gazzmaniac/Amiga-SMD-500/SMD500.sch

## KiCad design SMD500.sch (2019-11-12)

Schematic: SMD500.sch

Parts:
BT9: COINCELL; SMTU2032LF
C1, C2, C3, C4, C5, C6, C9, C11, C13, C14, C16, C17, C18, C19, C20, C21, C22, C23, C40, C41, C42, C301, C302, C305, C325, C335, C501, C502, C804: 0.33 uF; C_0805_2012Metric_Pad1.15x1.40mm_HandSolder
C7, C8, C10, C12, C15, C32, C33, C33.1, C34, C35, C36, C37, C39, C308, C701, C713, C800, C801, C802, C803: 0.01 uF; C_0805_2012Metric_Pad1.15x1.40mm_HandSolder
C45.1, C306, C712: 10 uF; CP_Elec_4x5.7
C45.2, C45.3, C321, C331, C450, C451, C711: 0.1 uF; C_0805_2012Metric_Pad1.15x1.40mm_HandSolder
C298, C299: 0.47 uF; C_0805_2012Metric_Pad1.15x1.40mm_HandSolder
C303, C304, C324, C334: 22 uF; CP_Elec_6.3x5.3
C307, C401, C402: 1000 uF; CAPAE1350X1400N
C311, C312, C313, C314: 0.047 uF; C_0805_2012Metric_Pad1.15x1.40mm_HandSolder
C322, C332: 6800 pF; C_0805_2012Metric_Pad1.15x1.40mm_HandSolder
C323, C333: 3900 pF; C_0805_2012Metric_Pad1.15x1.40mm_HandSolder
C403: 47 pF; C_0805_2012Metric_Pad1.15x1.40mm_HandSolder
C411, C412, C413, C421, C422, C423: 470 pF; C_0805_2012Metric_Pad1.15x1.40mm_HandSolder
C452: 0.1u; C_0805_2012Metric_Pad1.15x1.40mm_HandSolder
C453: 18 pF; C_0805_2012Metric_Pad1.15x1.40mm_HandSolder
C460: 33 pF; C_0805_2012Metric_Pad1.15x1.40mm_HandSolder
C461: 39 pF; C_0805_2012Metric_Pad1.15x1.40mm_HandSolder
C811, C812, C813, C814, C815, C816: 100 uF; CP_Elec_6.3x7.7
C821, C822: 47 uF; CP_Elec_6.3x7.7
C911: 22 pF; C_0805_2012Metric_Pad1.15x1.40mm_HandSolder
C913: 4.7 uF; EEEHB1E4R7AR
CE101, CE110, CE402, CE403, CE404, CE405, CE407, CE498, CE501, CE531, CE601, CE602, CE702, CE703, CE704: 0.01 uF; C_0805_2012Metric_Pad1.15x1.40mm_HandSolder
CE104, CE105: 68 pF; C_0805_2012Metric_Pad1.15x1.40mm_HandSolder
CE302, CE303, CE411, CE412, CE413, CE414, CE421, CE422, CE423, CE424: 6800 pF; C_0805_2012Metric_Pad1.15x1.40mm_HandSolder
CE401, CE408: 0.22 uF; C_0805_2012Metric_Pad1.15x1.40mm_HandSolder
CE402.2, CE402.3, CE402.4, CE402.5, CE403.1, CE403.3, CE403.4, CE431, CE432, CE433, CE434, CE499, CE511, CE512, CE513, CE514, CE515, CE516, CE517, CE518, CE519, CE521, CE522, CE523, CE524, CE525, CE532, CE533, CE534, CE535, CE536, CE537, CE538, CE611, CE612, CE613, CE614, CE615, CE616, CE617, CE618, CE619, CE620, CE621, CE622, CE623, CE624, CE625, CE626: 100 pF; C_0805_2012Metric_Pad1.15x1.40mm_HandSolder
CE441, CE442, CE443, CE444: 470 pF; C_0805_2012Metric_Pad1.15x1.40mm_HandSolder
CN1, CN2: DB9-M; D09P13B4PA00LF; MPN 5747840-3; Mouser Product D09P13B4PA00LF
CN3: PJRAN1X1U03AUX(RED); PJRAN1X1U03AUX; Mouser Part Number 502-PJRAN1X1U03AUX
CN4: PJRAN1X1U02AUX(WHITE); PJRAN1X1U03AUX; Mouser Part Number 502-PJRAN1X1U03AUX
CN5: DB23_Female_MountingHoles; DSUB-23_Female_Horizontal_P2.77x2.84mm_EdgePinOffset4.94mm_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
CN6: DB25P; D25P13B4PA00LF
CN7: DB25S; D25S33E4PA00LF
CN8: SQ&RNDDIN; A500 Power
CN9: DB23; DSUB-23_Male_Horizontal_P2.77x2.84mm_EdgePinOffset4.94mm_Ho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
CN10: PJRAN1X1U03AUX(YELLOW); PJRAN1X1U03AUX; Mouser Part Number 502-PJRAN1X1U03AUX
CN11: 2x17; PinHeader_2x17_P2.54mm_Vertical
CN12, CN14: 2-171825-4; TE_2-171825-4
CN13: 1x8HEADER; PinHeader_1x08_P2.54mm_Vertical
CN15, CN45: Conn_01x04; HDRV4W69P0X250_1X4_1000X500X1040P
D99, D912: 1N4148W-7-F; SOD3716X115N; Manufacturer_Part_Number 1N4148W-7-F; Mouser Part Number 621-1N4148W-F
D501: 1N914; D_DO-35_SOD27_P7.62mm_Horizontal
E101, E110, E402, E403, E404, E405, E406.1, E406.2, E407, E431, E432, E433, E498: FB200R; R_0805_2012Metric_Pad1.15x1.40mm_HandSolder
E102, E103, E106, E107, E108, E109: 47 pF; C_0805_2012Metric_Pad1.15x1.40mm_HandSolder
E305, E306: 270 pF; C_0805_2012Metric_Pad1.15x1.40mm_HandSolder
E435: FB; R_0805_2012Metric_Pad1.15x1.40mm_HandSolder
E501, E502, E503: 47R 0.5W; R_0805_2012Metric_Pad1.15x1.40mm_HandSolder
E631, E632: 100 pF; C_0805_2012Metric
E666: 22 pF; C_0805_2012Metric
E791, E792, E793, E794: 47 pF; C_0805_2012Metric
FB101: 68R@100MHz; R_0805_2012Metric_Pad1.15x1.40mm_HandSolder
FB102: 150R@100MHz; R_0805_2012Metric_Pad1.15x1.40mm_HandSolder
FB601, FB602, FB702, FB703, FB704: FB200R; R_0805_2012Metric_Pad1.15x1.40mm_HandSolder
FB802: FB; R_0805_2012Metric_Pad1.15x1.40mm_HandSolder
HY1: VIDEOHYBRID; PinHeader_1x22_P2.54mm_Vertical
JP1, JP10.1, JP10.2, JP98, JP199, JP450: SolderJumper_2_Bridged; SolderJumper-2_P1.3mm_Bridged_Pad1.0x1.5mm
JP2: SolderJumper_3_Bridged12_2; SolderJumper-3_P1.3mm_Bridged12_Pad1.0x1.5mm_NumberLabels
JP3.1, JP3.2: Jumper_2_Bridged; SolderJumper-2_P1.3mm_Bridged_Pad1.0x1.5mm
JP4.1, JP4.2, JP7.1, JP7.2, JP8, JP99.1, JP99.2: SolderJumper_3_Bridged12; SolderJumper-3_P1.3mm_Bridged12_Pad1.0x1.5mm_NumberLabels
JP9: SolderJumper_2_Open; SolderJumper-2_P1.3mm_Open_Pad1.0x1.5mm
JP11: SolderJumper_3_Bridged1-2; SolderJumper-3_P1.3mm_Bridged12_Pad1.0x1.5mm_NumberLabels
L450: 68uH; L_0805_2012Metric_Pad1.15x1.40mm_HandSolder
LF1: AmigaLineFilter; Amiga Line Filter
MT1, MT2, MT4, MT5, MT6, MT7: MountingHole_Pad; MountingHole_4mm_Pad_Via
P1: EDGE86; 86 pin edge connector
P9: Conn_02x28_Odd_Even; PinHeader_2x28_P2.54mm_Vertical(Mirror)
Q301, Q502, Q503: MMBT3906-TP; SOT-23-3; MPN MMBT3906-TP; Digi-Key_PN MMBT3906-TPCT-ND
Q321, Q331: PMBF4391
Q501, Q711: MMBT3904-TP; SOT-23-3; MPN MMBT3904-TP; Digi-Key_PN MMBT3904TPMSCT-ND
R101, R102: 27; R_0805_2012Metric_Pad1.15x1.40mm_HandSolder
R103, R104, R105, R106, R107, R113: 47; R_0805_2012Metric_Pad1.15x1.40mm_HandSolder
R109: 68R; R_0805_2012Metric_Pad1.15x1.40mm_HandSolder
R111, R112, R114: 68; R_0805_2012Metric_Pad1.15x1.40mm_HandSolder
R191, R192, R303, R304, R305, R324, R334, R713, R915, R916: 1K; R_0805_2012Metric_Pad1.15x1.40mm_HandSolder
R201, R202, R209, R402, R403, R404, R503, R504: 4.7K; R_0805_2012Metric_Pad1.15x1.40mm_HandSolder
R301, R302: 10R; R_0805_2012Metric_Pad1.15x1.40mm_HandSolder
R306, R308, R322, R323, R332, R333, R339, R501, R505, R506, R912, R914: 10K; R_0805_2012Metric_Pad1.15x1.40mm_HandSolder
R307, R502: 2.7K; R_0805_2012Metric_Pad1.15x1.40mm_HandSolder
R309: 1R 0.5W; R_0805_2012Metric_Pad1.15x1.40mm_HandSolder
R321, R331: 360R; R_0805_2012Metric_Pad1.15x1.40mm_HandSolder
R325, R335: 390R; R_0805_2012Metric_Pad1.15x1.40mm_HandSolder
R326, R336: 470K; R_0805_2012Metric_Pad1.15x1.40mm_HandSolder
R401, R406, R408: 4.7R 0.5W; R_0805_2012Metric_Pad1.15x1.40mm_HandSolder
R405: 0.47R 0.5W; R_0805_2012Metric_Pad1.15x1.40mm_HandSolder
R409: 150R; R_0805_2012Metric_Pad1.15x1.40mm_HandSolder
R450, R451, R452: 75R; R_0805_2012Metric_Pad1.15x1.40mm_HandSolder
R453, R455, R457: 300R; R_0805_2012Metric_Pad1.15x1.40mm_HandSolder
R454, R456, R458: 374R; R_0805_2012Metric_Pad1.15x1.40mm_HandSolder
R460: 200R; R_0805_2012Metric_Pad1.15x1.40mm_HandSolder
R461, R711: 1M; R_0805_2012Metric_Pad1.15x1.40mm_HandSolder
R507: 100R; R_0805_2012Metric_Pad1.15x1.40mm_HandSolder
R712: 47K; R_0805_2012Metric_Pad1.15x1.40mm_HandSolder
RE104, RE105, RE613, RE614, RE615, RE617, RE620, RE621, RE622, RE623, RE624, RE625: 27R; R_0805_2012Metric_Pad1.15x1.40mm_HandSolder
RE302, RE303, RE441, RE442, RE443, RE444: 0R; R_0805_2012Metric_Pad1.15x1.40mm_HandSolder
RE411, RE412, RE413, RE414, RE415, RE416, RE417, RE421, RE422, RE423, RE424, RE425, RE426, RE427, RE499, RE511, RE512, RE513, RE514, RE515, RE516, RE517, RE518, RE519, RE520, RE521, RE522, RE523, RE524, RE532, RE533, RE534, RE535, RE536, RE537, RE538, RE611, RE612, RE616, RE618, RE619, RE626: 68R; R_0805_2012Metric_Pad1.15x1.40mm_HandSolder
RE434, RE531: 47R; R_0805_2012Metric_Pad1.15x1.40mm_HandSolder
RP101.1, RP101.2, RP101.3, RP101.4, RP101.5, RP101.6, RP101.7, RP101.8, RP102.1, RP102.2, RP102.3, RP102.4, RP102.5, RP102.6, RP102.7, RP105.1, RP105.2, RP105.3, RP105.4, RP105.5, RP105.6, RP105.7, RP105.9, RP106.1, RP106.2, RP106.3, RP106.4, RP106.5, RP106.6, RP106.7, RP106.8, RP106.9, RP107.1, RP107.2, RP107.3, RP107.4, RP107.5, RP107.6, RP107.7, RP107.8, RP107.9, RP108.1, RP108.2, RP108.3, RP108.4, RP108.5, RP108.6, RP108.7, RP108.8, RP108.9, RP109.1, RP109.2, RP109.3, RP109.4, RP109.5, RP109.6, RP109.7, RP109.8, RP109.9, RP110.1, RP110.2, RP110.3, RP110.4, RP110.5, RP110.6, RP110.7, RP110.8, RP110.9, RP111.1, RP111.2, RP111.3, RP111.4, RP111.5, RP111.6, RP111.7, RP111.8, RP111.9, RP401.1, RP401.2, RP401.3, RP401.4, RP401.5, RP401.6, RP401.7, RP401.8: 4.7K; R_0805_2012Metric_Pad1.15x1.40mm_HandSolder
RP103.1, RP103.2, RP103.3, RP103.4: 39R; R_0805_2012Metric_Pad1.15x1.40mm_HandSolder
RP104.1, RP104.2, RP104.3, RP104.4, RP104.5, RP104.6, RP104.7, RP104.8, RP104.9: 470R; R_0805_2012Metric_Pad1.15x1.40mm_HandSolder
RP201.1, RP201.2, RP201.3, RP201.4, RP201.5, RP202.1, RP202.2, RP202.3, RP202.4, RP202.5, RP203.1, RP203.2, RP203.3, RP203.4, RP203.5: 68R; R_0805_2012Metric_Pad1.15x1.40mm_HandSolder
RP402.1, RP402.2, RP402.3, RP402.4, RP402.5, RP403.1, RP403.2, RP403.3, RP403.4, RP403.5: 47R; R_0805_2012Metric_Pad1.15x1.40mm_HandSolder
RP501.1, RP501.2, RP501.3, RP501.4, RP501.5, RP501.6, RP501.7, RP501.8: 10K; R_0805_2012Metric_Pad1.15x1.40mm_HandSolder
TC9: 8-40 pF (JZ400); C_Trimmer_Voltronics_JZ
TP9: TestPoint; TestPoint_Pad_1.0x1.0mm
U1: 68000D; DIP-64_W22.86mm_LongPads
U2.1: 8375_FatAgnus2MB; PLCC-84_THT-Socket
U2.2: 8372_FatAgnus1MB; PLCC-84_THT-Socket
U3: 8364_Paula; DIP-48_W15.24mm_LongPads
U4: 8373_DeniseECS; DIP-48_W15.24mm_LongPads
U5: 5719_Gary; DIP-48_W15.24mm_LongPads
U6: ROM_SOCKET; DIP-42_W15.24mm_Socket_LongPads
U7, U8: 8520_CIA; DIP-40_W15.24mm_LongPads
U9: RTC72421; DIP-18_W7.62mm_LongPads
U10, U12: SN74LS244DW; SOIC127P1030X265-20N; Manufacturer_Part_Number SN74LS241DW; Mouser Part Number 595-SN74LS241DW
U11, U13, U34: SN74LS373DW; SOIC127P1030X265-20N; Manufacturer_Part_Number SN74LS373DW; Mouser Part Number 595-SN74LS373DW
U14: TL084; SOIC127P600X175-14N
U15: SN74LS157DR
U16, U17, U18, U19, U20, U21, U22, U23: HYB514256B; DIP-20_W7.62mm_LongPads
U32: MC74AC139DR2G
U33: SN74F258D; SOIC127P600X175-16N; Manufacturer_Part_Number SN74F258D; Mouser Part Number 595-SN74F258D
U33.1: SN74F04DR
U35: N74F244D; SOIC127P1032X265-20N; Manufacturer_Part_Number N74F244D
U36: SN74LS05DR; SOIC127P600X175-14N
U37: 74LS32; SN74LS32NSR
U38: MAX1488ECSD+; SOIC127P600X175-14N; Manufacturer_Part_Number MAX1488ECSD+; Mouser Part Number 700-MAX1488ECSD
U39: MAX1489ECSD+; SOIC127P600X175-14N; Manufacturer_Part_Number MAX1489ECSD+; Mouser Part Number 700-MAX1489ECSD
U40, U41: SN74HCT245DWR; SOIC127P1030X265-20N
U42: NE555DR; SOIC127P600X175-8N; Manufacturer_Part_Number NE555DR; Mouser Part Number 595-NE555DR
U45: AD723ARUZ
U201: HYB5118160BSJ; SOJ-42
V1, V2, V3, V4, V5, V6, V7, V8, V9, V10, V11, V12, V13, V14, V15, V16, V17, V18, V19, V20: Conn_01x01_Male; SolderWirePad_1x01_Drill0.8mm
X1: ACO-28.37516MHz; Oscillator_DIP-14
Y9: LFXTAL002995Bulk; LFXTAL002995BULK; Manufacturer_Part_Number LFXTAL002995Bulk; Mouser Part Number 449-LFXTAL002995BULK
Y460: 17.734 475 MHz 18 pF; XTAL_HC49

Connections:
7MHZ: E103.1, P1.7, R106.1, U1.15 (CLK)
7MHZ_A: C403.1, E794.1, R107.1, U4.35 (7M)
28MHZ: E666.2, FB102.2, U2.1.34 (28MHz), U2.2.34 (28MHz)
+12V: C802.1, C821.1, CN12.4, CN14.4, E404.1, E502.1, FB602.1, FB704.1, LF1.5, P9.55, R301.1, U38.14 (VCC)
+AV: C301.1, C303.1, Q301.3 (E), R301.2, R307.2, U14.4 (V+)
+BATT: C9.1, C913.1, D99.1, D912.1, U9.18 (VCC)
+VID: C40.1, C41.1, C45.1.1, C45.2.1, C45.3.1, C402.1, HY1.2 (+VID), R406.1, U40.1 (DIR), U40.20 (VCC), U41.1 (DIR), U41.20 (VCC), U45.3 (CE), U45.4 (TERM), U45.13 (DVDD), U45.18 (TVDET), U45.22 (AVDD), U45.25 (AVDD1)
+VXX: C4.1, E405.1, E406.1.1, E406.2.1, R406.2, U4.19 (VCC)
-12V: C803.2, C822.2, E403.1, E503.1, FB703.1, LF1.6, P9.56, R302.2, U38.1 (VEE)
-AV: C302.2, C304.2, R302.1, R308.2, U14.11 (V-)
A1: P1.29, RP107.8.2, U1.29 (A1), U2.1.60 (A1), U2.2.60 (A1), U6.10 (A0)
A2: P1.27, P9.45, RP107.7.2, U1.30 (A2), U2.1.61 (A2), U2.2.61 (A2), U6.9 (A1), U9.4 (A0)
A3: P1.26, P9.46, RP107.6.2, U1.31 (A3), U2.1.62 (A3), U2.2.62 (A3), U6.8 (A2), U9.5 (A1)
A4: P1.24, P9.47, RP107.5.2, U1.32 (A4), U2.1.63 (A4), U2.2.63 (A4), U6.7 (A3), U9.6 (A2)
A5: P1.21, P9.48, RP107.4.2, U1.33 (A5), U2.1.64 (A5), U2.2.64 (A5), U6.6 (A4), U9.7 (A3)
A6: P1.23, RP107.3.2, U1.34 (A6), U2.1.65 (A6), U2.2.65 (A6), U6.5 (A5)
A7: P1.28, RP107.2.2, U1.35 (A7), U2.1.66 (A7), U2.2.66 (A7), U6.4 (A6)
A8: P1.30, RP107.1.2, U1.36 (A8), U2.1.67 (A8), U2.2.67 (A8), U6.3 (A7), U7.38 (RS0), U8.38 (RS0)
A9: P1.32, RP106.1.2, U1.37 (A9), U2.1.68 (A9), U2.2.68 (A9), U6.41 (A8), U7.37 (RS1), U8.37 (RS1)
A10: P1.34, RP106.2.2, U1.38 (A10), U2.1.69 (A10), U2.2.69 (A10), U6.40 (A9), U7.36 (RS2), U8.36 (RS2)
A11: P1.36, RP106.3.2, U1.39 (A11), U2.1.70 (A11), U2.2.70 (A11), U6.39 (A10), U7.35 (RS3), U8.35 (RS3)
A12: P1.38, RP106.4.2, U1.40 (A12), U2.1.71 (A12), U2.2.71 (A12), U6.38 (A11), U37.1
A13: P1.39, RP106.5.2, U1.41 (A13), U2.1.72 (A13), U2.2.72 (A13), U6.37 (A12), U37.4
A14: P1.41, RP106.6.2, U1.42 (A14), U2.1.73 (A14), U2.2.73 (A14), U6.36 (A13)
A15: P1.43, RP106.7.2, U1.43 (A15), U2.1.74 (A15), U2.2.74 (A15), U6.35 (A14), U36.13 (6A)
A16: P1.45, RP106.8.2, U1.44 (A16), U2.1.75 (A16), U2.2.75 (A16), U6.34 (A15)
A17: P1.47, RP105.7.2, U1.45 (A17), U2.1.76 (A17), U2.2.76 (A17), U5.33 (A17), U6.33 (A16)
A18: P1.52, RP105.6.2, U1.46 (A18), U2.1.77 (A18), U2.2.77 (A18), U5.34 (A18), U6.2 (A17)
A19: JP2.1 (A), P1.54, RP105.5.2, U1.47 (A19), U5.35 (A19), U6.1 (A18)
A20: P1.56, RP105.4.2, U1.48 (A20), U2.1.35 (A20), U5.36 (A20), U6.42 (A19)
A21: P1.58, RP105.3.2, U1.50 (A21), U5.37 (A21)
A22: P1.57, RP105.2.2, U1.51 (A22), U5.38 (A22)
A23: JP2.3 (B), P1.59, RP105.1.2, U1.52 (A23), U5.39 (A23)
AUDIN: C501.1, JP10.1.2 (B)
AUDIO: C301.2, C302.1, C303.2, C304.1, C305.2, C306.2, C308.2, C311.2, C312.2, C313.2, C314.2, C323.2, C333.2, E305.2, E306.2, FB802.2, R304.2, R325.2, R335.2, U3.34 (AGND)
AUDOUT: C502.1, JP10.2.2 (B)
B: C452.2, E433.2, HY1.17 (AB), R452.2
BDRA0: P9.23, RP201.5.1, U35.9 (YB3)
BDRA1: P9.24, RP201.4.1, U35.7 (YB2)
BDRA2: P9.25, RP201.3.1, U34.9 (4Q)
BDRA3: P9.26, RP201.2.1, U34.19 (8Q)
BDRA4: P9.27, RP201.1.1, U34.16 (7Q)
BDRA5: P9.28, RP202.4.1, U34.6 (3Q)
BDRA6: P9.29, RP202.3.1, U34.15 (6Q)
BDRA7: P9.30, RP202.2.1, U34.5 (2Q)
BDRA8: P9.31, RP202.1.1, U34.12 (5Q)
BDRA9: RP202.5.1, U32.2 (A0A), U32.14 (A0B), U34.2 (1Q)
BUSY: CE522.2, RE522.2, U8.2 (PA0), U8.39 (S)
CCK: E108.1, R103.1, U3.28 (CCK), U4.36 (CCK), U5.28 (CCK), U33.5 (2A), U33.6 (2B), U35.15 (IB1), U41.6 (A5)
CCKQ: E107.1, R104.1, U3.29 (CCKQ), U5.27 (CCKQ), U33.10 (3B), U33.11 (3A)
CCK_C: E402.1, RP403.2.2
CDAC: E793.1, P1.15, RP103.1.1
CHROMA: CN45.4, R456.2, U45.23 (C)
CLK_PAL: U33.1.4, U45.17 (4FSC)
COMP: E435.2, R454.2, U45.20 (CV)
CTS: CE535.2, RE535.2, U39.4 (IB)
D0: P1.75, P9.41, RP110.4.2, U1.5 (D0), U6.14 (D0), U7.33 (D0), U9.14 (D0), U10.2 (1A1), U11.2 (1Q)
D1: P1.77, P9.42, RP110.5.2, U1.4 (D1), U6.16 (D1), U7.32 (D1), U9.13 (D1), U10.4 (1A2), U11.5 (2Q)
D2: P1.79, P9.43, RP110.6.2, U1.3 (D2), U6.18 (D2), U7.31 (D2), U9.12 (D2), U10.6 (1A3), U11.6 (3Q)
D3: P1.81, P9.44, RP110.7.2, U1.2 (D3), U6.20 (D3), U7.30 (D3), U9.11 (D3), U10.8 (1A4), U11.9 (4Q)
D4: P1.83, RP110.8.2, U1.1 (D4), U6.23 (D4), U7.29 (D4), U10.11 (2A1), U11.12 (5Q)
D5: P1.86, RP110.3.2, U1.64 (D5), U6.25 (D5), U7.28 (D5), U10.13 (2A2), U11.15 (6Q)
D6: P1.84, RP110.2.2, U1.63 (D6), U6.27 (D6), U7.27 (D6), U10.15 (2A3), U11.16 (7Q)
D7: P1.82, RP110.1.2, U1.62 (D7), U6.29 (D7), U7.26 (D7), U10.17 (2A4), U11.19 (8Q)
D8: P1.80, RP108.8.2, U1.61 (D8), U6.15 (D8), U8.33 (D0), U12.2 (1A1), U13.2 (1Q)
D9: P1.78, RP108.7.2, U1.60 (D9), U6.17 (D9), U8.32 (D1), U12.4 (1A2), U13.5 (2Q)
D10: P1.76, RP108.6.2, U1.59 (D10), U6.19 (D10), U8.31 (D2), U12.6 (1A3), U13.6 (3Q)
D11: P1.71, RP108.5.2, U1.58 (D11), U6.21 (D11), U8.30 (D3), U12.8 (1A4), U13.9 (4Q)
D12: P1.69, RP108.4.2, U1.57 (D12), U6.24 (D12), U8.29 (D4), U12.11 (2A1), U13.12 (5Q)
D13: P1.67, RP108.3.2, U1.56 (D13), U6.26 (D13), U8.28 (D5), U12.13 (2A2), U13.15 (6Q)
D14: P1.65, RP108.2.2, U1.55 (D14), U6.28 (D14), U8.27 (D6), U12.15 (2A3), U13.16 (7Q)
D15: P1.63, RP108.1.2, U1.54 (D15), U6.30 (D15), U8.26 (D7), U12.17 (2A4), U13.19 (8Q)
DIR: CN11.18, RE623.1, U8.11 (PB1)
DKWE: U3.39 (DKWE), U5.8 (DKWE)
DMAL: U2.1.18 (DMAL), U2.2.18 (DMAL), U3.12 (DMAL)
DRA0: U2.1.42 (DRA0), U2.2.43 (DRA0), U35.11 (IB3)
DRA1: U2.1.43 (DRA1), U2.2.44 (DRA1), U35.13 (IB2)
DRA2: U2.1.44 (DRA2), U2.2.45 (DRA2), U34.8 (4D)
DRA3: U2.1.45 (DRA3), U2.2.46 (DRA3), U34.18 (8D)
DRA4: U2.1.46 (DRA4), U2.2.47 (DRA4), U34.17 (7D)
DRA5: U2.1.47 (DRA5), U2.2.48 (DRA5), U34.7 (3D)
DRA6: U2.1.48 (DRA6), U2.2.49 (DRA6), U34.14 (6D)
DRA7: U2.1.49 (DRA7), U2.2.50 (DRA7), U34.4 (2D)
DRA8: U2.1.50 (DRA8), U2.2.51 (DRA8), U34.13 (5D)
DRA9: U2.1.55 (DRA9), U34.3 (1D)
DRD0: P9.5, RP111.1.2, U2.1.14 (DRD0), U2.2.14 (DRD0), U3.10 (DRD0), U4.7 (DRD0), U10.18 (1Y1), U11.3 (1D), U16.18 (I/O3), U20.18 (I/O3), U201.4 (I/O3)
DRD1: P9.6, RP109.1.2, U2.1.13 (DRD1), U2.2.13 (DRD1), U3.9 (DRD1), U4.6 (DRD1), U10.16 (1Y2), U11.4 (2D), U16.2 (I/O2), U20.2 (I/O2), U201.3 (I/O2)
DRD2: P9.7, RP111.2.2, U2.1.12 (DRD2), U2.2.12 (DRD2), U3.7 (DRD2), U4.5 (DRD2), U10.14 (1Y3), U11.7 (3D), U16.19 (I/O4), U20.19 (I/O4), U201.5 (I/O4)
DRD3: P9.8, RP109.2.2, U2.1.11 (DRD3), U2.2.11 (DRD3), U3.6 (DRD3), U4.4 (DRD3), U10.12 (1Y4), U11.8 (4D), U16.1 (I/O1), U20.1 (I/O1), U201.2 (I/O1)
DRD4: P9.9, RP111.3.2, U2.1.10 (DRD4), U2.2.10 (DRD4), U3.5 (DRD4), U4.3 (DRD4), U10.9 (2Y1), U11.13 (5D), U17.18 (I/O3), U21.18 (I/O3), U201.9 (I/O7)
DRD5: P9.10, RP109.3.2, U2.1.9 (DRD5), U2.2.9 (DRD5), U3.4 (DRD5), U4.2 (DRD5), U10.7 (2Y2), U11.14 (6D), U17.2 (I/O2), U21.2 (I/O2), U201.8 (I/O6)
DRD6: P9.11, RP111.4.2, U2.1.8 (DRD6), U2.2.8 (DRD6), U3.3 (DRD6), U4.1 (DRD6), U10.5 (2Y3), U11.17 (7D), U17.19 (I/O4), U21.19 (I/O4), U201.10 (I/O8)
DRD7: P9.12, RP109.4.2, U2.1.7 (DRD7), U2.2.7 (DRD7), U3.2 (DRD7), U4.48 (DRD7), U10.3 (2Y4), U11.18 (8D), U17.1 (I/O1), U21.1 (I/O1), U201.7 (I/O5)
DRD8: P9.13, RP111.5.2, U2.1.6 (DRD8), U2.2.6 (DRD8), U3.1 (DRD8), U4.47 (DRD8), U12.18 (1Y1), U13.3 (1D), U18.18 (I/O3), U22.18 (I/O3), U201.35 (I/O11)
DRD9: P9.14, RP109.5.2, U2.1.5 (DRD9), U2.2.5 (DRD9), U3.48 (DRD9), U4.46 (DRD9), U12.16 (1Y2), U13.4 (2D), U18.2 (I/O2), U22.2 (I/O2), U201.34 (I/O10)
DRD10: P9.15, RP111.6.2, U2.1.4 (DRD10), U2.2.4 (DRD10), U3.47 (DRD10), U4.45 (DRD10), U12.14 (1Y3), U13.7 (3D), U18.19 (I/O4), U22.19 (I/O4), U201.36 (I/O12)
DRD11: P9.16, RP109.6.2, U2.1.3 (DRD11), U2.2.3 (DRD11), U3.46 (DRD11), U4.44 (DRD11), U12.12 (1Y4), U13.8 (4D), U18.1 (I/O1), U22.1 (I/O1), U201.33 (I/O9)
DRD12: P9.17, RP111.7.2, U2.1.2 (DRD12), U2.2.2 (DRD12), U3.45 (DRD12), U4.43 (DRD12), U12.9 (2Y1), U13.13 (5D), U19.18 (I/O3), U23.18 (I/O3), U201.40 (I/O15)
DRD13: P9.18, RP109.7.2, U2.1.1 (DRD13), U2.2.1 (DRD13), U3.44 (DRD13), U4.42 (DRD13), U12.7 (2Y2), U13.14 (6D), U19.2 (I/O2), U23.2 (I/O2), U201.39 (I/O14)
DRD14: P9.19, RP111.8.2, U2.1.84 (DRD14), U2.2.84 (DRD14), U3.43 (DRD14), U4.41 (DRD14), U12.5 (2Y3), U13.17 (7D), U19.19 (I/O4), U23.19 (I/O4), U201.41 (I/O16)
DRD15: P9.20, RP109.8.2, U2.1.83 (DRD15), U2.2.83 (DRD15), U3.42 (DRD15), U4.40 (DRD15), U12.3 (2Y4), U13.18 (8D), U19.1 (I/O1), U23.1 (I/O1), U201.38 (I/O13)
DSR: CE536.2, RE536.2, U39.10 (IC)
DTR: CE531.2, RE531.1, U38.11 (OUT_D)
E: P1.50, R109.2, U1.20 (E)
FC0: P1.31, RP102.1.2, U1.28 (FC0)
FC1: P1.33, RP102.2.2, U1.27 (FC1)
FC2: P1.35, RP102.3.2, U1.26 (FC2)
G: C451.2, E432.2, HY1.12 (AG), R451.2
GND: BT9.2 (-), C1.2, C2.2, C3.2, C4.2, C5.2, C6.2, C7.2, C8.2, C9.2, C10.2, C11.2, C12.2, C13.2, C14.2, C15.2, C16.2, C17.2, C18.2, C19.2, C20.2, C21.2, C22.2, C23.2, C32.2, C33.2, C33.1.2, C34.2, C35.2, C36.2, C37.2, C39.2, C40.2, C41.2, C42.2, C45.1.2, C45.2.2, C45.3.2, C298.2, C299.2, C307.2, C401.2, C402.2, C403.2, C411.2, C412.2, C413.2, C421.2, C422.2, C423.2, C453.1, C460.2, C461.1, C701.2, C711.2, C712.2, C713.2, C801.2, C802.2, C803.1, C804.2, C811.2, C812.2, C813.2, C814.2, C815.2, C816.2, C821.2, C822.1, C911.1, C913.2, CE104.2, CE105.2, CE302.1, CE303.1, CE401.1, CE402.1, CE402.2.1, CE402.3.1, CE402.4.1, CE402.5.1, CE403.1, CE403.1.1, CE403.3.1, CE403.4.1, CE404.1, CE405.1, CE408.1, CE411.2, CE412.1, CE413.1, CE414.2, CE421.1, CE422.1, CE423.1, CE424.2, CE431.1, CE432.1, CE433.1, CE434.1, CE441.1, CE442.1, CE443.1, CE444.1, CE498.1, CE499.1, CE501.1, CE511.1, CE512.1, CE513.1, CE514.1, CE515.1, CE516.1, CE517.1, CE518.1, CE519.1, CE521.1, CE522.1, CE523.1, CE524.1, CE525.1, CE531.1, CE532.1, CE533.1, CE534.1, CE535.1, CE536.1, CE537.1, CE538.1, CE601.1, CE602.1, CE611.2, CE612.2, CE613.2, CE614.2, CE615.2, CE616.2, CE617.1, CE618.1, CE619.1, CE620.1, CE621.1, CE622.1, CE623.1, CE624.1, CE625.1, CE626.1, CE702.2, CE703.2, CE704.2, CN1.0, CN1.8, CN2.0, CN2.8, CN3.1 (SLEEVE), CN4.1 (SLEEVE), CN5.0 (PAD), CN5.3, CN5.4, CN5.5, CN5.6, CN5.7, CN6.0 (PAD), CN6.7, CN7.0 (PAD), CN7.17, CN7.18, CN7.19, CN7.20, CN7.21, CN7.22, CN7.23, CN7.24, CN7.25, CN8.2 (SH), CN8.6 (SH), CN8.7 (SH), CN8.8 (SH), CN8.12 (SH), CN8.13 (SH), CN9.0 (PAD), CN9.13, CN9.16, CN9.17, CN9.18, CN9.19, CN9.20, CN10.1 (SLEEVE), CN11.1, CN11.5, CN11.7, CN11.9, CN11.11, CN11.13, CN11.15, CN11.17, CN11.19, CN11.21, CN11.23, CN11.25, CN11.27, CN11.29, CN11.31, CN11.33, CN12.2, CN12.3, CN13.6, CN14.2, CN14.3, CN15.4, CN45.1, CN45.2, D501.2 (A), E102.2, E103.2, E106.2, E107.2, E108.2, E109.2, E631.2, E632.2, E666.1, E791.2, E792.2, E793.2, E794.2, FB802.1, HY1.1 (GND), HY1.22 (GND), JP7.1.3 (B), JP9.2 (B), JP199.2 (B), LF1.8, MT1.1, MT2.1, MT4.1, MT5.1, MT6.1, MT7.1, P1.1, P1.2, P1.3, P1.4, P1.12, P1.13, P1.25, P1.37, P1.49, P1.61, P1.73, P1.85, P9.3, P9.4, P9.21, P9.22, P9.34, P9.53, P9.54, Q501.2 (E), Q711.2 (E), R409.2, R453.1, R455.1, R457.1, R501.2, RP101.8.2, RP102.7.2, RP104.9.2, RP105.9.2, RP106.9.2, RP107.9.2, RP108.9.2, RP109.9.2, RP110.9.2, RP111.9.2, TC9.2, U1.16 (GND), U1.53 (GND), U2.1.41 (GND), U2.1.58 (GND), U2.1.82 (GND), U2.2.42 (GND), U2.2.58 (GND), U2.2.82 (GND), U3.8 (GND), U4.37 (GND), U5.1 (GND), U5.24 (GND), U5.40 (NC), U6.11 (_CS), U6.12 (GND), U6.31 (GND), U7.1 (GND), U8.1 (GND), U9.9 (GND), U10.10 (GND), U11.10 (GND), U12.10 (GND), U13.10 (GND), U15.8 (GND), U15.15 (*G), U16.16 (_OE), U16.20 (GND), U17.16 (_OE), U17.20 (GND), U18.16 (_OE), U18.20 (GND), U19.16 (_OE), U19.20 (GND), U20.16 (_OE), U20.20 (GND), U21.16 (_OE), U21.20 (GND), U22.16 (_OE), U22.20 (GND), U23.16 (_OE), U23.20 (GND), U32.8 (GND), U33.8 (GND), U33.15 (~OE), U33.1.7 (GND), U34.1 (~OC), U34.10 (GND), U35.1 (~OEA), U35.10 (GND), U35.19 (~OEB), U36.7 (GND), U37.7 (GND), U37.10, U37.13, U38.7 (GND), U39.7 (GND), U40.10 (GND), U40.19 (~OE), U41.10 (GND), U41.19 (~OE), U42.1 (GND), U45.1 (STND), U45.2 (SA), U45.8 (AGND), U45.12 (TGND), U45.14 (DGND), U45.28 (AGND), U201.22 (GND), U201.29 (_OE), U201.37 (GND), U201.42 (GND), V1.1, V2.1, V3.1, V4.1, V5.1, V6.1, V7.1, V8.1, V9.1, V10.1, V11.1, V12.1, V13.1, V14.1, V15.1, V16.1, V17.1, V18.1, V19.1, V20.1, X1.1 (NC), X1.7 (GND)
LEFT: C321.2, E306.1, R321.2, U3.31 (AUDA[LEFT]), U14.13 (-)
LUMA: CN45.3, R458.2, U45.26 (Y)
M0H: RE443.1, U4.9 (M0H)
M0V: RE441.1, U4.38 (M0V)
M1H: RE442.1, U4.8 (M1H)
M1V: RE444.1, U4.39 (M1V)
unnamed: BT9.1 (+), D99.2
unnamed: C2.1, CE101.2, E101.1, U2.1.15 (VCC), U2.2.15 (VCC)
unnamed: C3.1, C307.1, R303.1, R309.2, U3.27 (VCC)
unnamed: C33.1, C33.1.1, CE407.2, E407.1, U33.16 (VCC), U33.1.14 (VCC)
unnamed: C308.1, Q301.2 (C), R308.1, R326.2, R336.2
unnamed: C321.1, Q321.1 (D), R321.1, R322.2, U14.14
unnamed: C322.1, C324.1, C325.2, U14.1, U14.2 (-)
unnamed: C322.2, R322.1, R323.2
unnamed: C323.1, Q321.2 (S), R323.1, U14.3 (+)
unnamed: C324.2, C325.1, JP10.2.1 (A), R324.2
unnamed: C331.1, Q331.1 (D), R331.1, R332.2, U14.8
unnamed: C332.1, C334.1, C335.2, U14.6 (-), U14.7
unnamed: C332.2, R332.1, R333.2
unnamed: C333.1, Q331.2 (S), R333.1, U14.5 (+)
unnamed: C334.2, C335.1, R334.2
unnamed: C401.1, HY1.21 (VCC), R405.2
unnamed: C411.1, CN1.6, RE415.1
unnamed: C412.1, CN1.5, RE417.1
unnamed: C413.1, CN1.9, RE416.1
unnamed: C421.1, CN2.6, RE425.1
unnamed: C422.1, CN2.5, RE427.1
unnamed: C423.1, CN2.9, RE426.1
unnamed: C450.1, U45.5 (RIN)
unnamed: C451.1, U45.6 (GIN)
unnamed: C452.1, U45.7 (BIN)
unnamed: C453.2, L450.2
unnamed: C460.1, R461.1, U33.1.1, Y460.1
unnamed: C461.2, R460.2, Y460.2
unnamed: C501.2, CN6.18
unnamed: C502.2, CN6.11
unnamed: C701.1, CE110.2, E110.1, X1.14 (Vcc)
unnamed: C711.1, R711.2, U42.2 (TRIG)
unnamed: C712.1, R712.2, U42.6 (THRES)
unnamed: C713.1, U42.5 (CONT)
unnamed: C800.1, CN8.5 (-12v), LF1.3
unnamed: C800.2, CN8.1 (+5V), CN8.10 (+5V), LF1.2
unnamed: C911.2, JP99.2.3 (B), Y9.1
unnamed: CE302.2, CN4.2 (TIP), CN4.3 (SHUNT), RE302.1
unnamed: CE303.2, CN3.2 (TIP), CN3.3 (SHUNT), RE303.1
unnamed: CE401.2, CN1.7, R401.1
unnamed: CE402.2, CN9.15, E402.2
unnamed: CE402.2.2, CN9.6, RP402.2.1
unnamed: CE402.3.2, CN9.7, RP402.3.1
unnamed: CE402.4.2, CN9.8, RP402.4.1
unnamed: CE402.5.2, CN9.9, RP402.5.1
unnamed: CE403.2, CN9.21, E403.2
unnamed: CE403.3.2, CN9.11, RP403.3.1
unnamed: CE403.4.2, CN9.12, RP403.4.1
unnamed: CE404.2, CN9.22, E404.2
unnamed: CE405.2, CN9.23, E405.2
unnamed: CE408.2, CN2.7, R408.2
unnamed: CE411.1, CN1.1, RE411.2
unnamed: CE412.2, CN1.2, RE412.2
unnamed: CE413.2, CN1.3, RE413.2
unnamed: CE414.1, CN1.4, RE414.2
unnamed: CE421.2, CN2.1, RE421.2
unnamed: CE422.2, CN2.2, RE422.2
unnamed: CE423.2, CN2.3, RE423.2
unnamed: CE424.1, CN2.4, RE424.2
unnamed: CE431.2, CN9.3, E431.1
unnamed: CE432.2, CN9.4, E432.1
unnamed: CE433.2, CN9.5, E433.1
unnamed: CE434.2, CN9.10, RE434.1
unnamed: CE441.2, RE441.2, U15.4 (1Y)
unnamed: CE442.2, RE442.2, U15.12 (4Y)
unnamed: CE443.2, RE443.2, U15.7 (2Y)
unnamed: CE444.2, RE444.2, U15.9 (3Y)
unnamed: CE498.2, CN9.14, E498.2
unnamed: CE511.2, CN7.1, RE511.1
unnamed: CE512.2, CN7.2, RE512.1
unnamed: CE513.2, CN7.3, RE513.1
unnamed: CE514.2, CN7.4, RE514.1
unnamed: CE515.2, CN7.5, RE515.1
unnamed: CE516.2, CN7.6, RE516.1
unnamed: CE517.2, CN7.7, RE517.1
unnamed: CE518.2, CN7.8, RE518.1
unnamed: CE519.2, CN7.9, RE519.1
unnamed: CE525.2, CN7.16, RE520.2
unnamed: CE532.2, CN6.2, RE532.1
unnamed: CE533.2, CN6.4, RE533.1
unnamed: CE534.2, RE534.2, U39.1 (IA)
unnamed: CE537.2, RE537.2, U39.13 (ID)
unnamed: CE538.2, CN6.22, RE538.2
unnamed: CE601.2, CN5.12, FB601.2
unnamed: CE602.2, CN5.23, FB602.2
unnamed: CE611.1, CN5.1, RE611.1
unnamed: CE612.1, CN5.2, RE612.1
unnamed: CE613.1, CN5.8, RE613.1
unnamed: CE614.1, CN5.9, RE614.1
unnamed: CE615.1, CN5.10, RE615.1
unnamed: CE616.1, CN5.11, RE616.1
unnamed: CE617.2, CN5.13, RE617.2
unnamed: CE618.2, CN5.14, RE618.2
unnamed: CE619.2, CN5.15, RE619.2
unnamed: CE620.2, CN5.16, RE620.2
unnamed: CE621.2, CN5.17, RE621.2
unnamed: CE622.2, CN5.18, RE622.2
unnamed: CE623.2, CN5.19, RE623.2
unnamed: CE624.2, CN5.20, RE624.2
unnamed: CE625.2, CN5.21, RE625.2
unnamed: CE626.2, CN5.22, RE626.2
unnamed: CE702.1, FB702.2, P1.5, P1.6
unnamed: CE703.1, FB703.2, P1.8
unnamed: CE704.1, FB704.2, P1.10
unnamed: CN6.3, RE534.1
unnamed: CN6.5, RE535.1
unnamed: CN6.6, RE536.1
unnamed: CN6.8, RE537.1
unnamed: CN6.9, E502.2
unnamed: CN6.10, E503.2
unnamed: CN6.20, RE531.2
unnamed: CN7.10, RE521.1
unnamed: CN7.11, RE522.1
unnamed: CN7.12, RE523.1
unnamed: CN7.13, RE524.1
unnamed: CN7.14, E501.1
unnamed: CN8.3 (+12V), CN8.9 (+12V), LF1.4
unnamed: CN8.4 (GND), LF1.1
unnamed: CN9.1, RP403.1.1
unnamed: CN9.2, RE499.1
unnamed: CN10.2 (TIP), CN10.3 (SHUNT), E435.1, R409.1
unnamed: CN13.7, Q502.2 (C), R507.1
unnamed: CN13.8, Q503.2 (C)
unnamed: D501.1 (K), Q501.1 (B), R501.1, R502.1
unnamed: FB101.1, X1.8 (OUT)
unnamed: FB101.2, U33.13 (4B)
unnamed: FB102.1, U33.12 (4Y)
unnamed: HY1.3 (R3), RP402.5.2, U40.18 (B1)
unnamed: HY1.4 (R2), U40.17 (B2)
unnamed: HY1.5 (R1), U40.16 (B3)
unnamed: HY1.6 (R0), U40.15 (B4)
unnamed: HY1.8 (G3), RP402.4.2, U40.14 (B5)
unnamed: HY1.9 (G2), U40.13 (B6)
unnamed: HY1.10 (G1), U40.12 (B7)
unnamed: HY1.11 (G0), U40.11 (B8)
unnamed: HY1.13 (B3), RP402.3.2, U41.18 (B1)
unnamed: HY1.14 (B2), U41.17 (B2)
unnamed: HY1.15 (B1), U41.16 (B3)
unnamed: HY1.16 (B0), RP402.2.2, U41.15 (B4)
unnamed: HY1.18 (CSYNC), U41.11 (B8)
unnamed: HY1.20 (SYNC), JP11.3 (B)
unnamed: JP1.2 (B), Q711.3 (C)
unnamed: JP2.2 (C), U2.1.59 (A19), U2.2.59 (A19)
unnamed: JP3.1.1 (A), U35.18 (YA0)
unnamed: JP3.2.2 (B), U35.16 (YA1)
unnamed: JP4.1.2 (C), U35.14 (YA2)
unnamed: JP4.2.2 (C), U35.12 (YA3)
unnamed: JP7.1.1 (A), P9.32
unnamed: JP7.2.2 (C), U7.19 (TICK)
unnamed: JP9.1 (A), P9.33, R916.2, U36.11 (5A), U36.12 (6Y)
unnamed: JP10.1.1 (A), R339.1
unnamed: JP11.1 (A), RP403.5.2
unnamed: JP11.2 (C), RE434.2
unnamed: JP98.1 (A), R201.2, RP203.2.2, U16.5 (NC), U17.5 (NC), U18.5 (NC), U19.5 (NC), U20.4 (_RAS), U20.5 (NC), U21.4 (_RAS), U21.5 (NC), U22.4 (_RAS), U22.5 (NC), U23.4 (_RAS), U23.5 (NC), U201.14 (_RAS)
unnamed: JP98.2 (B), R202.2, RP203.3.2, U16.4 (_RAS), U17.4 (_RAS), U18.4 (_RAS), U19.4 (_RAS)
unnamed: JP99.1.2 (C), U9.16 (XT)
unnamed: JP99.1.3 (B), TC9.1, Y9.2
unnamed: JP99.2.2 (C), U9.17 (_XT)
unnamed: JP199.1 (A), U2.2.41 (TEST)
unnamed: JP450.1 (A), L450.1
unnamed: JP450.2 (B), U45.21 (YTRAP)
unnamed: Q301.1 (B), R306.1, R307.1
unnamed: Q321.3 (G), R326.1
unnamed: Q331.3 (G), R336.1
unnamed: Q502.1 (B), R503.1
unnamed: Q503.1 (B), R504.1
unnamed: Q711.1 (B), R713.1
unnamed: R101.1, U5.43 (_DTACK)
unnamed: R102.1, U5.2 (_VPA)
unnamed: R103.2, U2.1.39 (CCK), U2.2.40 (CCK)
unnamed: R104.2, U2.1.38 (CCKQ), U2.2.39 (CCKQ)
unnamed: R105.2, U2.1.36 (_CDAC), U2.2.37 (_CDAC)
unnamed: R106.2, R107.2, U2.1.37 (7MHz), U2.2.38 (7MHz)
unnamed: R109.1, U7.25 (E), U8.25 (E)
unnamed: R111.1, U5.25 (_LATCH)
unnamed: R111.2, U11.11 (C), U13.11 (C)
unnamed: R112.1, U5.3 (_OEL)
unnamed: R112.2, U11.1 (~OC), U13.1 (~OC)
unnamed: R113.1, U5.4 (_OEB)
unnamed: R113.2, U10.1 (~1G), U10.19 (~2G), U12.1 (~1G), U12.19 (~2G)
unnamed: R114.1, U5.21 (_ROMEN)
unnamed: R306.2, U38.3 (OUT_A)
unnamed: R324.1, R325.1, RE302.2
unnamed: R334.1, R335.1, RE303.2
unnamed: R450.1, U45.9 (RT)
unnamed: R451.1, U45.10 (GT)
unnamed: R452.1, U45.11 (BT)
unnamed: R453.2, R454.1, U45.19 (CVSET)
unnamed: R455.2, R456.1, U45.24 (CSET)
unnamed: R457.2, R458.1, U45.27 (YSET)
unnamed: R460.1, R461.2, U33.1.2, U33.1.3
unnamed: R713.2, U42.3 (OUT)
unnamed: R912.2, TP9.1, U9.1 (STD.P)
unnamed: R914.2, U9.3 (ALE), U9.15 (_CS1)
unnamed: R915.2, U9.2 (_CS0), U36.10 (5Y)
unnamed: RE104.2, RP103.3.2, U33.7 (2Y)
unnamed: RE105.2, RP103.2.2, U33.9 (3Y)
unnamed: RE411.1, RP401.8.2, U15.3 (1B)
unnamed: RE412.1, RP401.6.2, U15.6 (2B)
unnamed: RE413.1, RP401.7.2, U15.2 (1A)
unnamed: RE414.1, RP401.5.2, U15.5 (2A)
unnamed: RE421.1, RP401.4.2, U15.10 (3B)
unnamed: RE422.1, RP401.2.2, U15.13 (4B)
unnamed: RE423.1, RP401.3.2, U15.11 (3A)
unnamed: RE424.1, RP401.1.2, U15.14 (4A)
unnamed: RE511.2, RP501.4.2, U7.18 (_PC)
unnamed: RE532.2, U38.8 (OUT_C)
unnamed: RP103.1.2, U33.4 (1Y)
unnamed: RP103.4.1, U33.1.12
unnamed: RP103.4.2, U2.2.35 (XCLK)
unnamed: RP203.1.2, U16.3 (_WE), U17.3 (_WE), U18.3 (_WE), U19.3 (_WE), U20.3 (_WE), U21.3 (_WE), U22.3 (_WE), U23.3 (_WE), U201.13 (_WE)
unnamed: RP203.4.1, U16.17 (_CAS), U17.17 (_CAS), U20.17 (_CAS), U21.17 (_CAS), U201.31 (_LCAS)
unnamed: RP203.5.2, U18.17 (_CAS), U19.17 (_CAS), U22.17 (_CAS), U23.17 (_CAS), U201.30 (_UCAS)
unnamed: RP402.1.2, U41.13 (B6)
unnamed: RP403.2.1, U41.14 (B5)
unnamed: RP403.5.1, U41.12 (B7)
unnamed: U4.20 (R0), U40.5 (A4)
unnamed: U4.21 (R1), U40.4 (A3)
unnamed: U4.22 (R2), U40.3 (A2)
unnamed: U4.23 (R3), U40.2 (A1)
unnamed: U4.24 (B0), U41.5 (A4)
unnamed: U4.25 (B1), U41.4 (A3)
unnamed: U4.26 (B2), U41.3 (A2)
unnamed: U4.27 (B3), U41.2 (A1)
unnamed: U4.28 (G0), U40.9 (A8)
unnamed: U4.29 (G1), U40.8 (A7)
unnamed: U4.30 (G2), U40.7 (A6)
unnamed: U4.31 (G3), U40.6 (A5)
unnamed: U4.33 (PIXELSW), U41.7 (A6)
unnamed: U32.1 (*EA), U32.15 (*EB), U34.11 (C), U35.5 (YB1)
unnamed: U5.47 (MTRX), U36.1 (1A)
unnamed: U5.46 (MTRON), U36.3 (2A)
unnamed: U5.45 (DKWDB), U36.5 (3A)
unnamed: U5.44 (DKWEB), U36.9 (4A)
unnamed: U8.8 (PA6), U38.4 (IN_B1)
unnamed: U8.9 (PA7), U38.12 (IN_D2)
unnamed: U8.6 (PA4), U39.6 (OB)
unnamed: U8.5 (PA3), U39.8 (OC)
unnamed: U8.7 (PA5), U39.11 (OD)
OVL: RP101.7.2, U5.30 (_OVL), U7.2 (PA0)
PIXELSW: E498.1, RP402.1.1
POT0X: C311.1, RE417.2, U3.32 (P0X)
POT0Y: C312.1, RE416.2, U3.33 (P0Y)
POT1X: C313.1, RE427.2, U3.35 (P1X)
POT1Y: C314.1, RE426.2, U3.36 (P1Y)
POUT: CE523.2, RE523.2, U8.3 (PA1), U8.40 (C)
PPD0: RE512.2, U7.10 (PB0)
PPD1: RE513.2, U7.11 (PB1)
PPD2: RE514.2, U7.12 (PB2)
PPD3: RE515.2, U7.13 (PB3)
PPD4: RE516.2, U7.14 (PB4)
PPD5: RE517.2, U7.15 (PB5)
PPD6: RE518.2, U7.16 (PB6)
PPD7: RE519.2, U7.17 (PB7)
R: C450.2, E431.2, HY1.7 (AR), R450.2
RAMA0: RP201.5.2, U16.6 (A0), U17.6 (A0), U18.6 (A0), U19.6 (A0), U20.6 (A0), U21.6 (A0), U22.6 (A0), U23.6 (A0), U201.17 (A0)
RAMA1: RP201.4.2, U16.7 (A1), U17.7 (A1), U18.7 (A1), U19.7 (A1), U20.7 (A1), U21.7 (A1), U22.7 (A1), U23.7 (A1), U201.18 (A1)
RAMA2: RP201.3.2, U16.8 (A2), U17.8 (A2), U18.8 (A2), U19.8 (A2), U20.8 (A2), U21.8 (A2), U22.8 (A2), U23.8 (A2), U201.19 (A2)
RAMA3: RP201.2.2, U16.9 (A3), U17.9 (A3), U18.9 (A3), U19.9 (A3), U20.9 (A3), U21.9 (A3), U22.9 (A3), U23.9 (A3), U201.20 (A3)
RAMA4: RP201.1.2, U16.11 (A4), U17.11 (A4), U18.11 (A4), U19.11 (A4), U20.11 (A4), U21.11 (A4), U22.11 (A4), U23.11 (A4), U201.23 (A4)
RAMA5: RP202.4.2, U16.12 (A5), U17.12 (A5), U18.12 (A5), U19.12 (A5), U20.12 (A5), U21.12 (A5), U22.12 (A5), U23.12 (A5), U201.24 (A5)
RAMA6: RP202.3.2, U16.13 (A6), U17.13 (A6), U18.13 (A6), U19.13 (A6), U20.13 (A6), U21.13 (A6), U22.13 (A6), U23.13 (A6), U201.25 (A6)
RAMA7: RP202.2.2, U16.14 (A7), U17.14 (A7), U18.14 (A7), U19.14 (A7), U20.14 (A7), U21.14 (A7), U22.14 (A7), U23.14 (A7), U201.26 (A7)
RAMA8: RP202.1.2, U16.15 (A8), U17.15 (A8), U18.15 (A8), U19.15 (A8), U20.15 (A8), U21.15 (A8), U22.15 (A8), U23.15 (A8), U201.27 (A8)
RAMA9: R209.2, RP202.5.2, U201.28 (A9)
RGA1: U2.1.33 (RGA1), U2.2.33 (RGA1), U3.26 (RGA1), U4.17 (RGA1)
RGA2: U2.1.32 (RGA2), U2.2.32 (RGA2), U3.25 (RGA2), U4.16 (RGA2)
RGA3: U2.1.31 (RGA3), U2.2.31 (RGA3), U3.24 (RGA3), U4.15 (RGA3)
RGA4: U2.1.30 (RGA4), U2.2.30 (RGA4), U3.23 (RGA4), U4.14 (RGA4)
RGA5: U2.1.29 (RGA5), U2.2.29 (RGA5), U3.22 (RGA5), U4.13 (RGA5)
RGA6: U2.1.28 (RGA6), U2.2.28 (RGA6), U3.21 (RGA6), U4.12 (RGA6)
RGA7: U2.1.27 (RGA7), U2.2.27 (RGA7), U3.20 (RGA7), U4.11 (RGA7)
RGA8: U2.1.26 (RGA8), U2.2.26 (RGA8), U3.19 (RGA8), U4.10 (RGA8)
RI: R502.2, RE538.1
RIGHT: C331.2, E305.1, R331.2, R339.2, U3.30 (AUDB[RIGHT]), U14.9 (-)
RTS: RE533.2, U38.6 (OUT_B)
R_W: P1.68, RP101.5.2, U1.9 (R/W), U2.1.22 (R/W), U2.2.22 (R/W), U5.12 (R/W), U7.22 (R/W), U8.22 (R/W)
SEL: CE524.2, Q501.3 (C), RE524.2, RP501.6.2, U8.4 (PA2)
VCC: C1.1, C5.1, C6.1, C7.1, C8.1, C10.1, C11.1, C12.1, C13.1, C14.1, C15.1, C16.1, C17.1, C18.1, C19.1, C20.1, C21.1, C22.1, C23.1, C32.1, C34.1, C35.1, C36.1, C37.1, C39.1, C42.1, C298.1, C299.1, C801.1, C804.1, C811.1, C812.1, C813.1, C814.1, C815.1, C816.1, CE101.1, CE110.1, CE407.1, CE501.2, CN12.1, CN13.4, CN14.1, D912.2, E101.2, E110.2, E406.1.2, E406.2.2, E407.2, E501.2, FB601.1, FB702.1, JP99.1.1 (A), JP99.2.1 (A), LF1.7, P9.1, P9.2, P9.51, P9.52, Q502.3 (E), Q503.3 (E), R191.1, R192.1, R201.1, R202.1, R209.1, R305.1, R309.1, R401.2, R402.1, R403.1, R404.1, R405.1, R408.1, R505.1, R506.1, R507.2, R711.1, R712.1, R912.1, R914.1, R915.1, R916.1, RP101.1.1, RP101.2.1, RP101.3.1, RP101.4.1, RP101.5.1, RP101.6.1, RP101.7.1, RP101.8.1, RP102.1.1, RP102.2.1, RP102.3.1, RP102.4.1, RP102.5.1, RP102.6.1, RP102.7.1, RP104.1.1, RP104.2.1, RP104.3.1, RP104.4.1, RP104.5.1, RP104.6.1, RP104.7.1, RP104.8.1, RP104.9.1, RP105.1.1, RP105.2.1, RP105.3.1, RP105.4.1, RP105.5.1, RP105.6.1, RP105.7.1, RP105.9.1, RP106.1.1, RP106.2.1, RP106.3.1, RP106.4.1, RP106.5.1, RP106.6.1, RP106.7.1, RP106.8.1, RP106.9.1, RP107.1.1, RP107.2.1, RP107.3.1, RP107.4.1, RP107.5.1, RP107.6.1, RP107.7.1, RP107.8.1, RP107.9.1, RP108.1.1, RP108.2.1, RP108.3.1, RP108.4.1, RP108.5.1, RP108.6.1, RP108.7.1, RP108.8.1, RP108.9.1, RP109.1.1, RP109.2.1, RP109.3.1, RP109.4.1, RP109.5.1, RP109.6.1, RP109.7.1, RP109.8.1, RP109.9.1, RP110.1.1, RP110.2.1, RP110.3.1, RP110.4.1, RP110.5.1, RP110.6.1, RP110.7.1, RP110.8.1, RP110.9.1, RP111.1.1, RP111.2.1, RP111.3.1, RP111.4.1, RP111.5.1, RP111.6.1, RP111.7.1, RP111.8.1, RP111.9.1, RP401.1.1, RP401.2.1, RP401.3.1, RP401.4.1, RP401.5.1, RP401.6.1, RP401.7.1, RP401.8.1, RP501.1.1, RP501.2.1, RP501.3.2, RP501.4.1, RP501.5.1, RP501.6.1, RP501.7.1, RP501.8.1, U1.14 (VCC), U1.49 (VCC), U5.6 (VCC), U5.17 (VCC), U5.48 (VCC), U6.22 (VCC), U6.32 (_BYTE), U7.20 (VCC), U8.20 (VCC), U10.20 (VCC), U11.20 (VCC), U12.20 (VCC), U13.20 (VCC), U15.16 (VCC), U16.10 (VCC), U17.10 (VCC), U18.10 (VCC), U19.10 (VCC), U20.10 (VCC), U21.10 (VCC), U22.10 (VCC), U23.10 (VCC), U32.16 (VCC), U34.20 (VCC), U35.20 (VCC), U36.14 (VCC), U37.14 (VCC), U38.5 (IN_B2), U38.10 (IN_C1), U38.13 (IN_D1), U39.14 (VCC), U42.4 (~RESET), U42.8 (VCC), U201.1 (VCC), U201.6 (VCC), U201.21 (VCC)
VREF: C305.1, C306.1, R303.2, R304.1, U14.10 (+), U14.12 (+)
XCLK: CE403.1.2, R404.2, RP403.1.2, U33.14 (4A), U33.1.13
XRDY: CN15.3, P1.18, RP104.7.2, U5.31 (XRDY)
_ACK: CE521.2, RE521.2, RP501.5.2, U7.24 (_F)
_AS: P1.74, RP101.6.2, U1.6 (AS), U2.1.24 (_AS), U2.2.24 (_AS), U5.13 (_AS)
_BCASL(0): JP4.1.1 (A), RP203.4.2, U32.4 (*O0A)
_BCASL(1): JP4.1.3 (B), P9.35, U32.5 (*O1A)
_BCASU(0): JP4.2.1 (A), RP203.5.1, U32.12 (*O0B)
_BCASU(1): JP4.2.3 (B), P9.36, U32.11 (*O1B)
_BEER: P1.46, RP104.4.2, U1.22 (BERR)
_BG: P1.64, U1.11 (BG)
_BGACK: P1.62, RP104.5.2, U1.12 (BGACK), U5.14 (_BGACK)
_BLISS: U2.1.19 (_BLISS), U2.2.19 (_BLISS), U5.19 (_BLISS)
_BLIT: U2.1.20 (_BLIT), U2.2.20 (_BLIT), U5.15 (_BLIT)
_BR: P1.60, RP104.6.2, U1.13 (BR)
_BRAS(0): JP3.1.2 (B), P9.38, RP203.2.1
_BRAS(1): JP3.2.1 (A), P9.37, RP203.3.1
_BWE: P9.39, RP203.1.1, U35.3 (YB0)
_CASL: U2.1.53 (_CASL), U2.2.54 (_CASL), U32.3 (A1A), U35.6 (IA2)
_CASU: U2.1.54 (_CASU), U2.2.55 (_CASU), U32.13 (A1B), U35.8 (IA3)
_CCK: E792.1, P1.16, RP103.3.1
_CCKQ: E791.1, P1.14, RP103.2.1
_CCKQ_A: CE105.1, E109.1, RE105.1, U15.1 (*A/B)
_CCK_A: CE104.1, E102.1, P9.40, RE104.1
_CDAC: E106.1, R105.1, U4.34 (_CDAC), U5.26 (_CDAC), U33.2 (1A), U33.3 (1B)
_CHNG: CN11.2, RE616.2, U7.4 (PA2)
_CLKRD: P9.49, U5.22 (_CLKRD), U9.8 (_RD)
_CLKWR: P9.50, U5.23 (_CLKWR), U9.10 (_WR)
_CSYNC: U2.1.80 (_CSYNC), U2.2.80 (_CSYNC), U4.32 (BLANK), U41.8 (A7), U41.9 (A8)
_DKRD: CN11.30, R305.2, RE612.2, U3.37 (_DKRD)
_DKWD: U3.38 (_DKWD), U5.9 (_DKWD)
_DKWDB: CN11.22, RE621.1, U36.6 (3Y)
_DKWEB: CN11.24, RE620.1, U36.8 (4Y)
_DTACK: P1.66, R101.2, RP104.1.2, U1.10 (DTACK)
_EVEN_CIA: U8.23 (_CS), U37.6
_EXTICK: JP7.1.2 (C), JP7.2.3 (B), RP501.7.2, U5.32 (_EXRAM)
_FIRE0: JP8.3 (B), RE415.2, U7.8 (PA6)
_FIRE1: JP8.1 (A), RE425.2, U7.9 (PA7)
_HLT: P1.55, RP101.1.2, U1.17 (HALT), U5.42 (_HLT)
_HSYNC: R402.2, RP403.3.2, U2.1.81 (_HSYNC), U2.2.81 (_HSYNC), U8.19 (TICK), U45.15 (HSYNC)
_INDEX: CN11.8, RE626.1, RP501.3.1, U8.24 (_F)
_INT2: CN15.1, P1.19, R191.2, U3.16 (_INT2), U7.21 (_INT)
_INT3: U2.1.17 (_INTR), U2.2.17 (_INTR), U3.17 (_INT3)
_INT6: P1.22, R192.2, U3.18 (_INT6), U8.21 (_INT)
_IORESET: RE520.1, RE615.2, U37.8
_IPL0: P1.40, RP102.4.2, U1.25 (IPL0), U3.13 (_IPL0)
_IPL1: P1.42, RP102.5.2, U1.24 (IPL1), U3.14 (_IPL1)
_IPL2: P1.44, RP102.6.2, U1.23 (IPL2), U3.15 (_IPL2)
_KBCLOCK: CN13.1, E632.1, RP501.2.2, U7.40 (C)
_KBDATA: CN13.2, E631.1, RP501.1.2, U7.39 (S)
_KBRESET: CN13.3, JP1.1 (A), RP501.8.2, U5.5 (_KBRESET)
_LDS: P1.70, RP101.3.2, U1.8 (LDS), U2.1.51 (_LDS), U2.2.52 (_LDS), U5.10 (_LDS)
_LED: R503.2, R505.2, U7.3 (PA1), U38.2 (IN_A)
_LPEN: JP8.2 (C), U2.1.78 (_LPEN), U2.2.78 (_LPEN)
_MTR: U5.7 (_MTR), U8.17 (PB7)
_MTR0: CN11.4, CN11.16, R504.2, R506.2, U36.4 (2Y)
_MTRX: RE613.2, U36.2 (1Y)
_ODD_CIA: U7.23 (_CS), U37.3
_OVR: CN15.2, P1.17, RP104.8.2, U5.29 (_OVR)
_RAMEN: U2.1.25 (_RAMEN), U2.2.25 (_RAMEN), U5.20 (_RAMEN)
_RAS(0): U2.1.57 (_RAS0), U2.2.57 (_RAS0), U35.2 (IA0)
_RAS(1): U2.1.56 (_RAS1), U2.2.56 (_RAS1), U35.4 (IA1)
_RDY: CN11.34, RE611.2, U7.7 (PA5)
_REGEN: U2.1.23 (_REGEN), U2.2.23 (_REGEN), U5.18 (_REGEN)
_RESET: U7.34 (_RESET), U8.34 (_RESET), U37.9, U37.11
_ROMEN: R114.2, U6.13 (_OE)
_RST: P1.53, RP101.2.2, U1.18 (RESET), U2.1.16 (_RESET), U2.2.16 (_RESET), U3.11 (_RESET), U5.41 (_RESET), U37.12
_RXD: U3.41 (_RxD), U39.3 (OA)
_SEL0: CN11.10, U5.16 (_SEL), U8.13 (PB3)
_SEL1: CN11.12, RE625.1, U8.14 (PB4)
_SEL2: RE614.2, U8.15 (PB5)
_SEL3: RE624.1, U8.16 (PB6)
_SIDE: CN11.32, RE617.1, U8.12 (PB2)
_STEP: CN11.20, RE622.1, U8.10 (PB0)
_TRK0: CN11.26, RE619.1, U7.6 (PA4)
_TXD: U3.40 (_TxD), U38.9 (IN_C2)
_UDS: P1.72, RP101.4.2, U1.7 (UDS), U2.1.52 (_UDS), U2.2.53 (_UDS), U5.11 (_UDS)
_VMA: P1.51, RP104.3.2, U1.19 (VMA), U37.2, U37.5
_VPA: P1.48, R102.2, RP104.2.2, U1.21 (VPA)
_VSYNC: JP7.2.1 (A), RP403.4.2, U2.1.79 (_VSYNC), U2.2.79 (_VSYNC), U45.16 (VSYNC)
_WE: U2.1.21 (_WE), U2.2.21 (_WE), U35.17 (IB0)
_WPROT: CN11.28, RE618.1, U7.5 (PA3)
_XCLKEN: CE499.2, R403.2, RE499.2, U2.2.36 (_XCLKEN), U33.1 (~A/B)

Notes on the sheet:
MEMORY EXPANSION
ROM
REAL TIME CLOCK
Y9, TC9, C911 not required with RTC72421. Change JP99.1 & JP99.2 and install Y9, TC9, & C911 if using MSM6462B
Only required if U9A requires external crystal
RTC POWER
BT9 changed to coin/button cell. Removed charging circuit and added D99 to prevent charging.
PAGE 8
NOTES
PAGE 2
PAGE 3
CHIP RAM
VIDEO POWER
AUDIO POWER
PAGE 4
MOUSE/JOYSTICK PORTS
AUDIO FILTERS
PAGE 5
PAGE6
PAGE 7
PARALLEL PORT
SERIAL PORT
RS232 DECOUPLING
EXTERNAL FLOPPY
INTERNAL FLOPPY
DECOUPLING
POWER UP RESET
KB CONN.
EXPANSION BUS
BUFFERED RESETS
EXPANSION BUS TERMINATION AND PULLUPS
CLOCK DISTRO
RP105-RP111 ARE OPTIONAL FOR INTERNAL BUS
PAGE 9
POWER INPUT
FCC GOOBERS
GROUNDED HOLES, &C.
GROUNDING HOLES FOR CN1, 2, 5, 6, 7, 9 ON CONNECTOR
PAGE 10
SMD 500 Project
ADDED OPTION FOR ONE HYB5118160BSJ 1Mx16BIT CHIP RAM IC REMOVED A501+ (PP12&13) FROM THESE SCHEMATICS (CONNECTOR P9 IS STILL THERE) CHANGED BT9 TO COIN CELL AND DIODE MINOR MODIFICATION TO ALLOW RTC72421 ADDED OPTION FOR AGNUS 8372. CHANGE JP2 FOR 8572 AND INSTALL FB101.1 ADD OPTION FOR ROUND DIN P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
ONLY POPULATE EITHER U201 (2 MB SMD HYB5118160BSJ 1Mx16) OR U16-23 (256Kx4 TTH FROM A500+). POPULATE C297-C299 FOR U201 POPULATE C16-C23 AND R209 FOR U16-U23 DO NOT INSTALL TRAP DOOR RAM WHEN U24 IS POPULATED IF USING 1 MB AGNUS DO NOT INSTALL TRAP DOOR WHEN U20-23 ARE POPULATED JUMPERS SET TO USE 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
1 MB AGNUS OPTION ONLY CONNECT ONE!
COMPOSITE & SVIDEO
RAM NOTES
IDE I/F
DRIVE POWER
SPARES
JP199 IS JP4 ON A500 R6 SCHEMATIC
VSYNC
HSYNC
CSYNC
BLUE
GREEN
RED
_XCLKEN
XCLK
VIDEO
+12
-12
GND
_CCK
PIXELSW
DGND
DO NOT POPULATE R409
_STROBE
_ACK
BUSY
POUT
SEL
_ERR
AUTO
_INIT
SEL1
TxD
RxD
RTS
CTS
DSR
sCD
sCTS
CLK
SQD
DTR
sRTS
RxC
sRxD
TxC
sTxD
INUSE
STATUS
GROUND
KEY
RESET
KBDATA
KBCLOCK
_RDY
_RD
_MTRX
_SEL2
_RESET
_CHNG
INDEX
_SEL1
_SEL3
_DIR
_STEP
_WE
_TRK0
_WPROT
SIDE
_CONFIG
